Conman2288/Braille-Printer/Version 1/Side plate wheel.SLDPRT

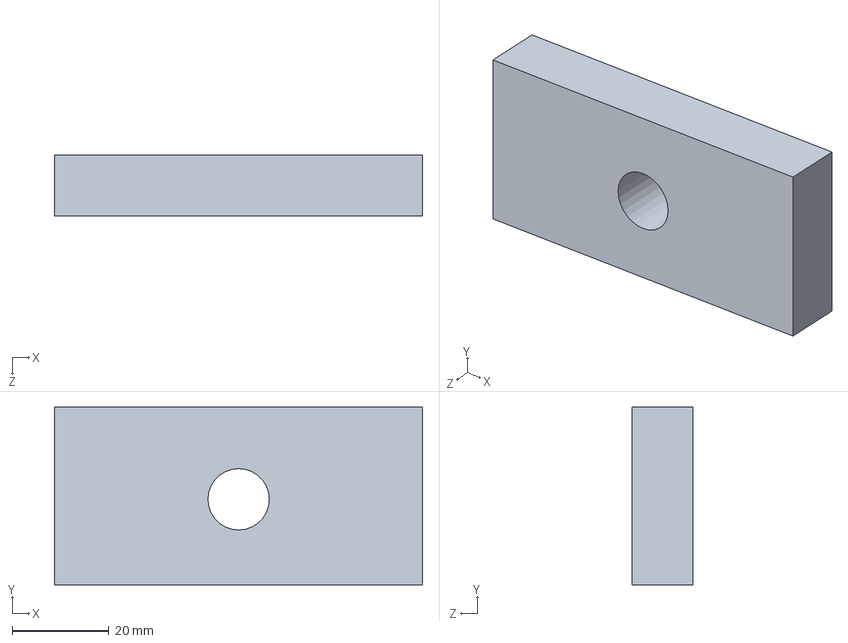
[picture p15: CAD file, 2023-03-29, an earlier design]
Version 1/Side plate wheel.SLDPRT
76.1 x 36.7 x 12.7 mm
