Conman2288/Braille-Printer/Version 1/Initial Assembly - Leadscrew portion.SLDASM

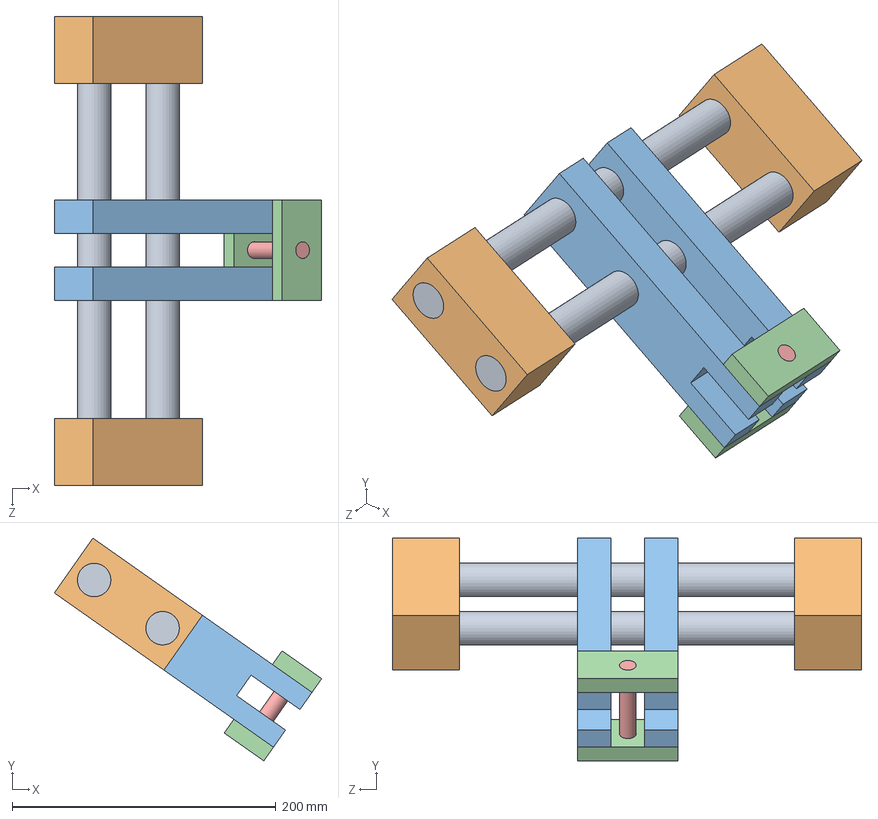
[picture p16: CAD file, 2023-03-29, an earlier design]
Version 1/Initial Assembly - Leadscrew portion.SLDASM
202.7 x 168.9 x 355.6 mm
leadscrew x 2
Leadscrew Holder x 2
Wheel holder x 2
Side plate wheel x 2
Wheel Axle
