Conman2288/Braille-Printer/Version 1/leadscrew.SLDPRT

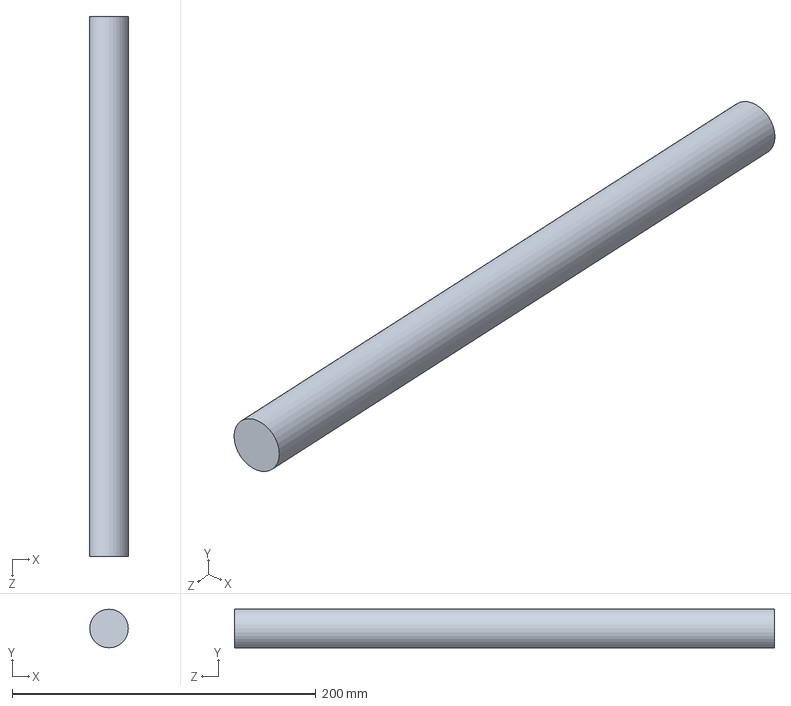
[picture p17: CAD file, 2023-03-29, an earlier design]
Version 1/leadscrew.SLDPRT
25.4 x 25.4 x 355.6 mm
