Conman2288/Braille-Printer/Version 1/Leadscrew Holder.SLDPRT

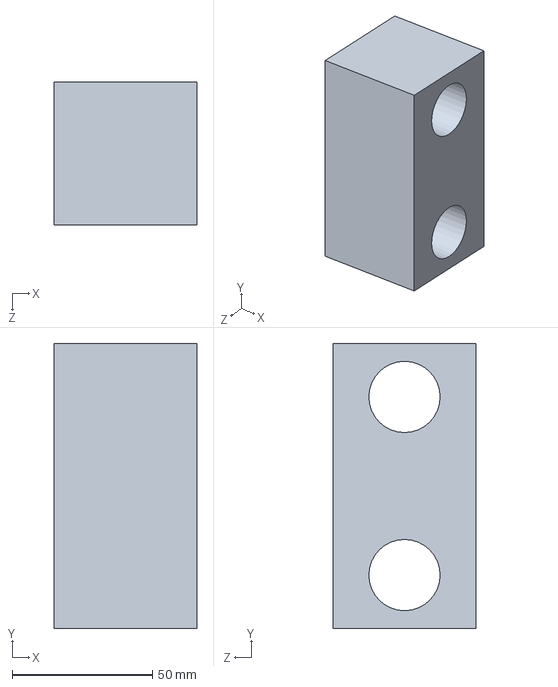
[picture p18: CAD file, 2023-03-29, an earlier design]
Version 1/Leadscrew Holder.SLDPRT
50.8 x 101.6 x 50.8 mm
